joshvillbrandt/mecanumbot-ros-pkg/extra/Mecanumbot Electrical Block Diagram.jpg

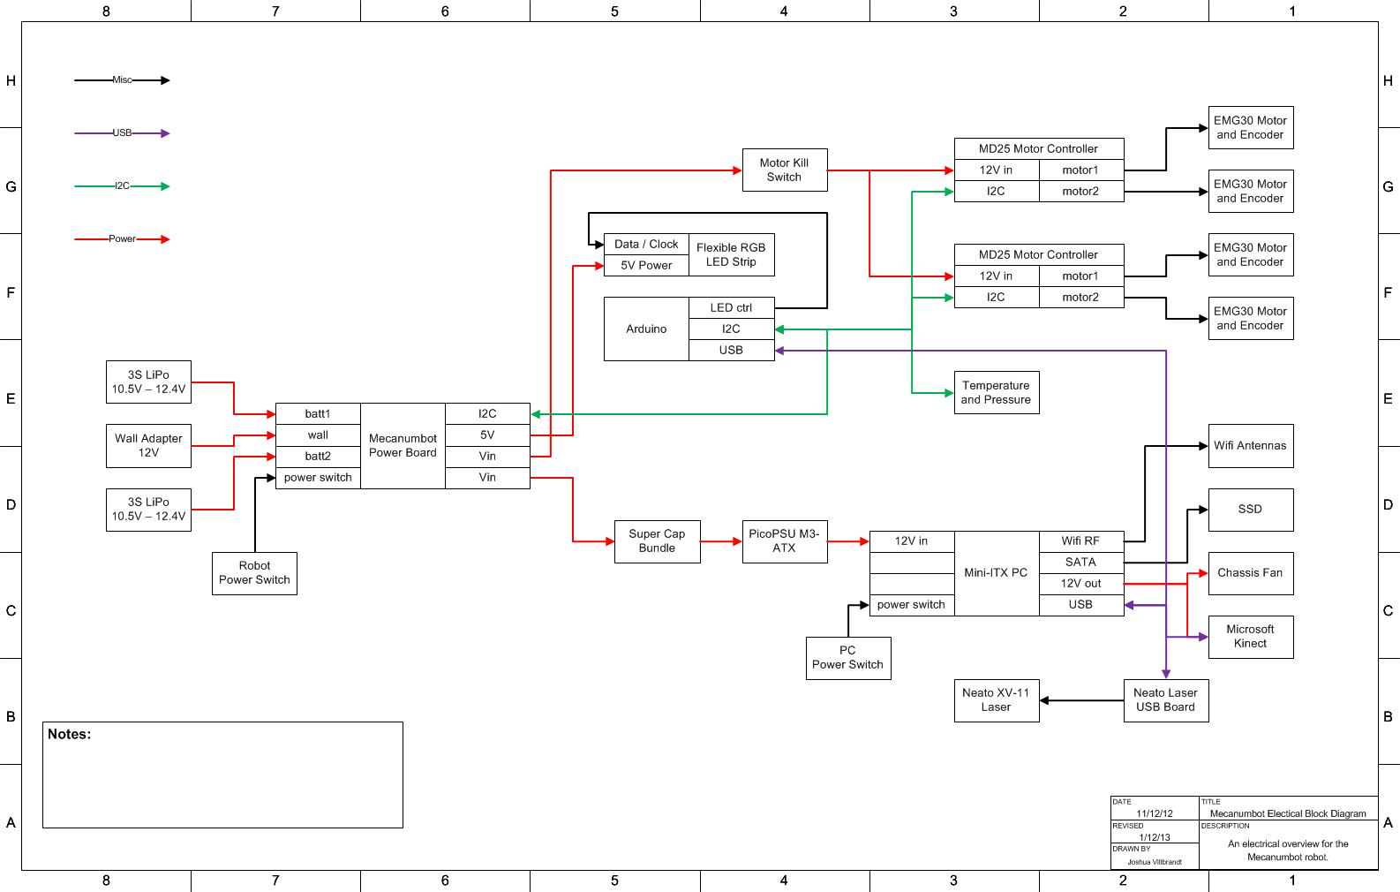
extra/Mecanumbot Electrical Block Diagram.jpg
