joshvillbrandt/mecanumbot-ros-pkg/maps/hector_slam_map_apartment_upstairs.jpg

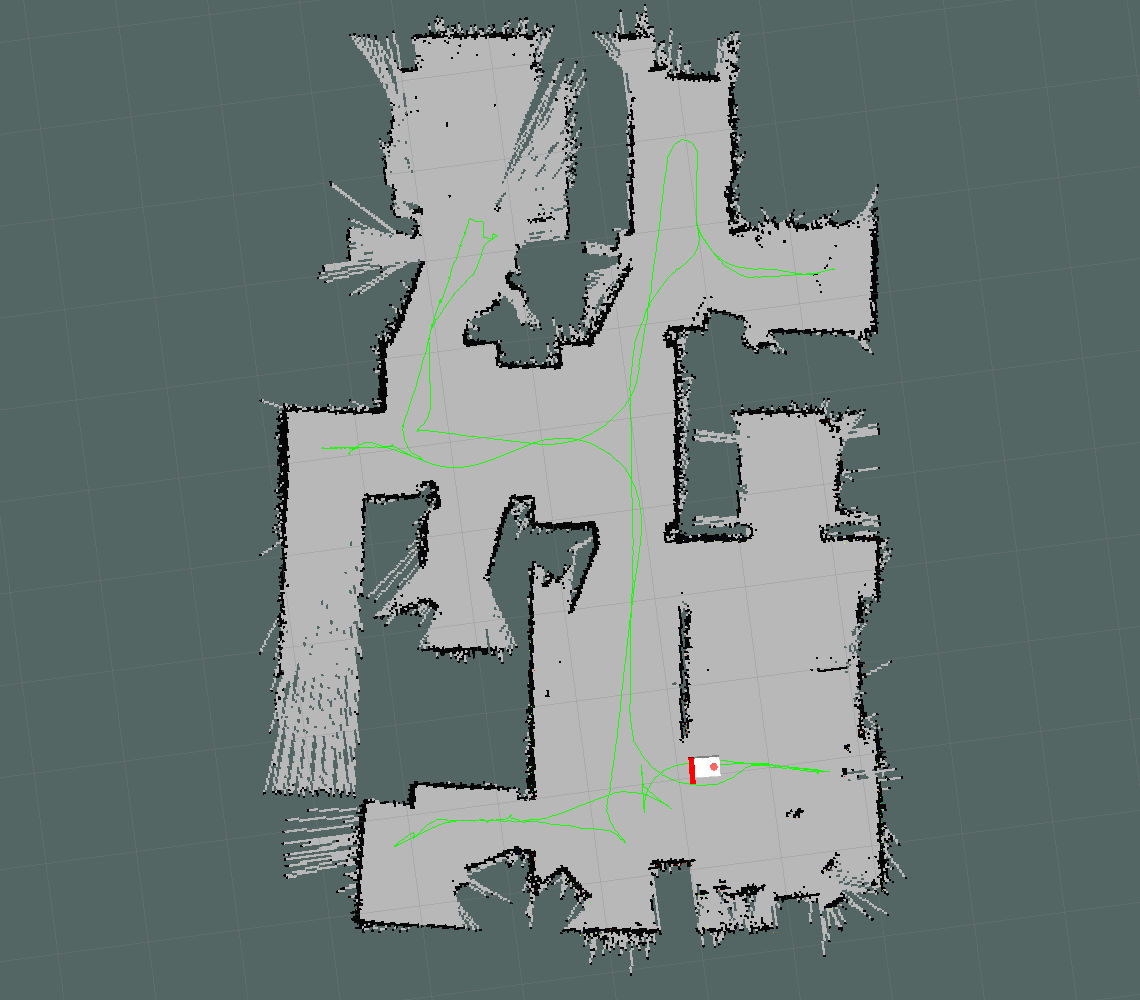
maps/hector_slam_map_apartment_upstairs.jpg
